xiaoxiae/Clis/01-scanning/03-convert.py

import argparse
import os
import sys
from glob import glob
from subprocess import DEVNULL, Popen

sys.path.append("..")
from config import *
from utilities import *

os.chdir(os.path.dirname(os.path.abspath(__file__)))

printer = Printer("convert")

parser = argparse.ArgumentParser()

parser.add_argument(
    "-k",
    "--keep",
    help="Keep the originals",
    action="store_true",
)

arguments = parser.parse_args()

for folder in sorted(glob(os.path.join(SCAN_PATH, "*"))):
    viewing_printed = False

    for file in sorted(glob(os.path.join(folder, "*"))):
        if not file.lower().endswith(IMAGE_EXTENSION):
            continue

        if not viewing_printed:
            viewing_printed = True
            printer.full(f"viewing {folder}.")

        printer.begin(f"converting file {os.path.basename(file)}")
        Popen(
            [
                "darktable-cli",
                file,
                os.path.join(os.path.dirname(file), "."),
                "--out-ext",
                CONVERTED_IMAGE_EXTENSION,
            ],
            stdin=DEVNULL,
            stdout=DEVNULL,
            stderr=DEVNULL,
        ).communicate()

        if not arguments.keep:
            printer.mid("removing the original")
            os.remove(file)

        printer.end("done.")
